vlinGit/Macropad/MacroPad/98db0589-fdbe-4938-8a90-1729ba8583cc.png

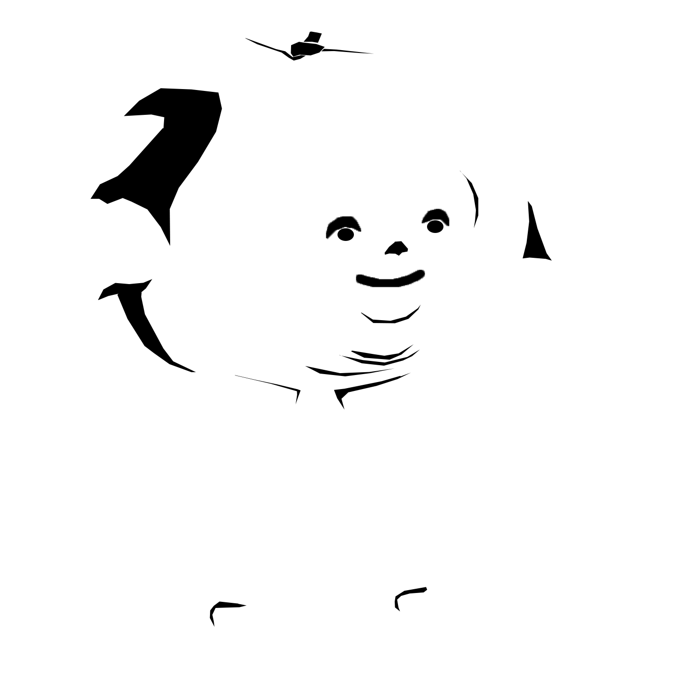
MacroPad/98db0589-fdbe-4938-8a90-1729ba8583cc.png
