vlinGit/Macropad/MacroPad/marbastlib-main/marbastlib-main/resources/repolist.png

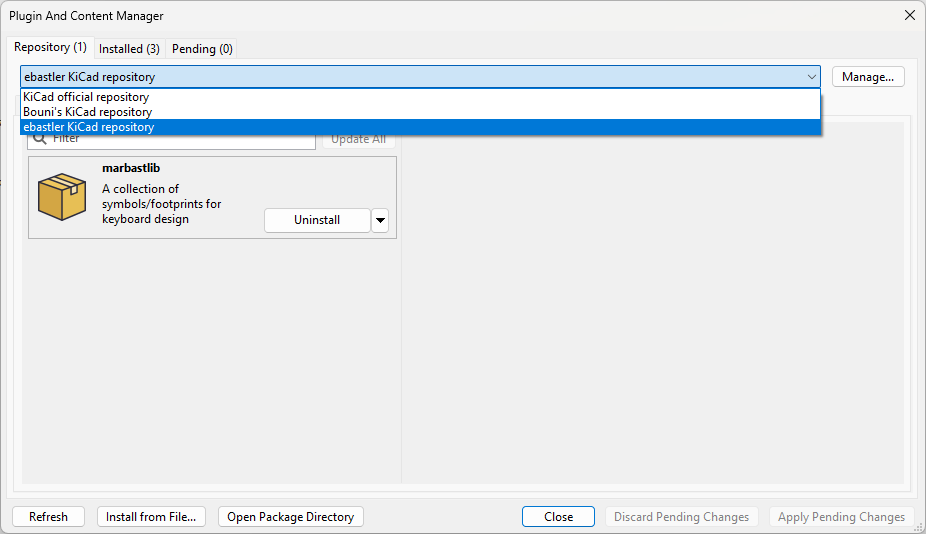
MacroPad/marbastlib-main/marbastlib-main/resources/repolist.png
