vlinGit/Macropad/MacroPad/simplePumpkin.png

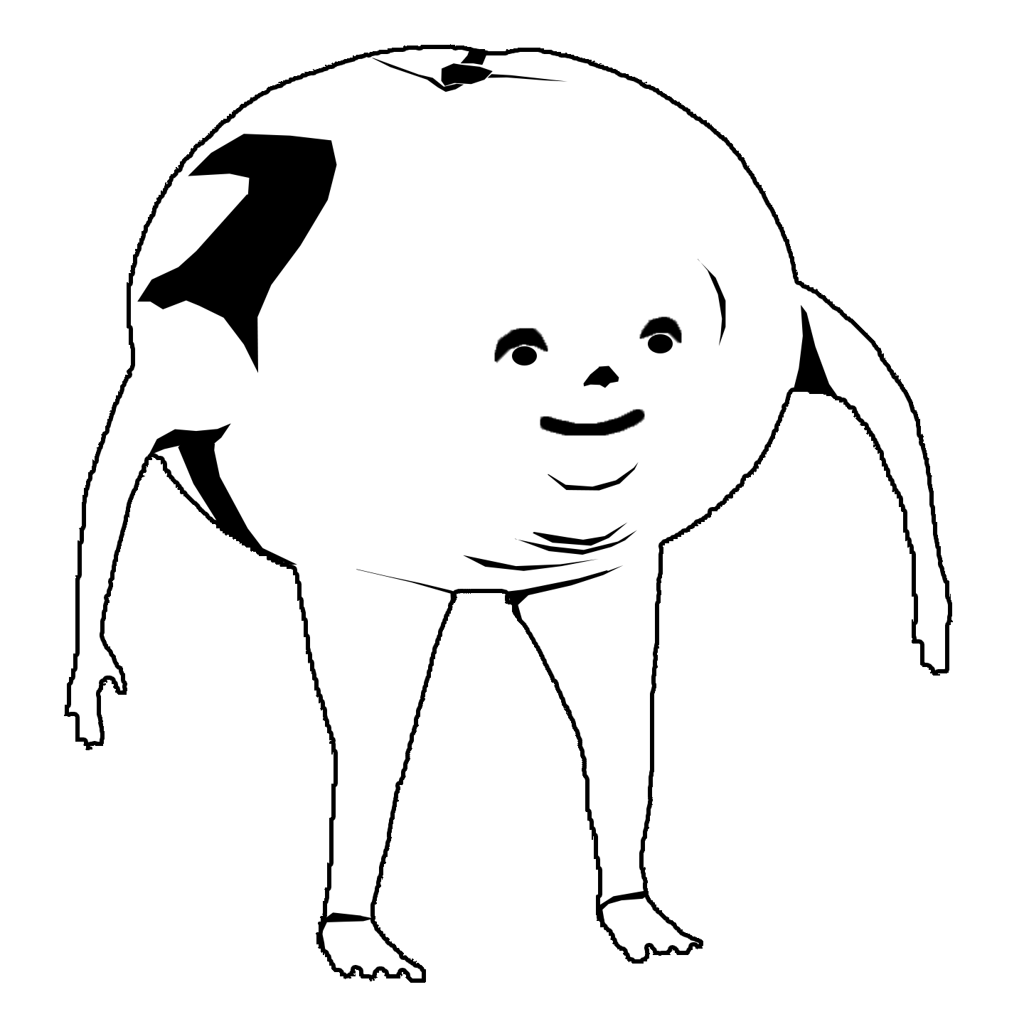
MacroPad/simplePumpkin.png
