vlinGit/Macropad/MacroPad/marbastlib-main/marbastlib-main/3dmodels/SW_SKHLLC.step

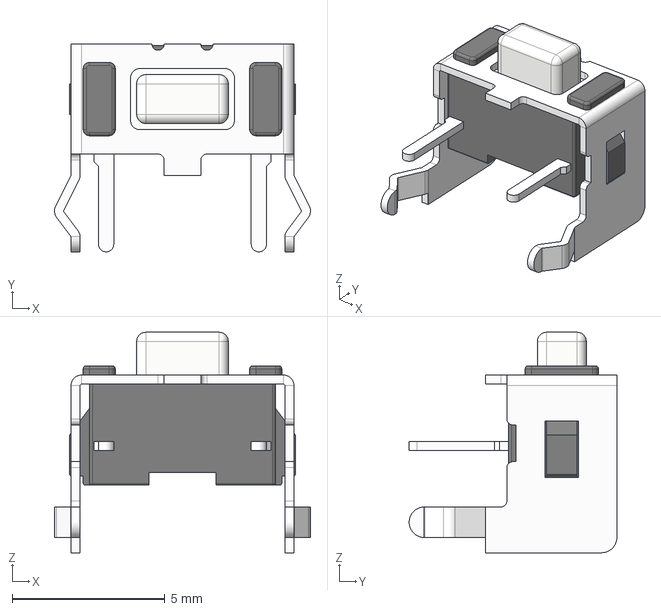
[picture p29: CAD file, 2024-05-07]
MacroPad/marbastlib-main/marbastlib-main/3dmodels/SW_SKHLLC.step
8.38 x 6.80 x 7.22 mm
