vlinGit/Macropad/MacroPad/marbastlib-main/marbastlib-main/3dmodels/SW_SSSS213100.step

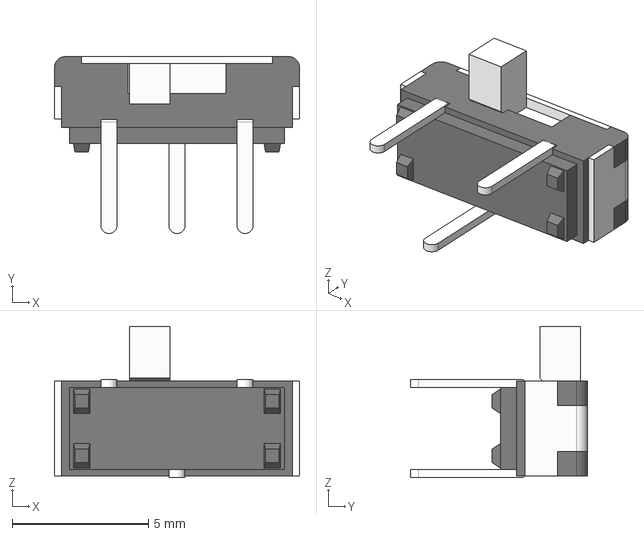
[picture p30: CAD file, 2024-05-07]
MacroPad/marbastlib-main/marbastlib-main/3dmodels/SW_SSSS213100.step
9.00 x 6.50 x 5.55 mm
