vlinGit/Macropad/MacroPad/marbastlib-main/marbastlib-main/3dmodels/PNT_psp1000.step

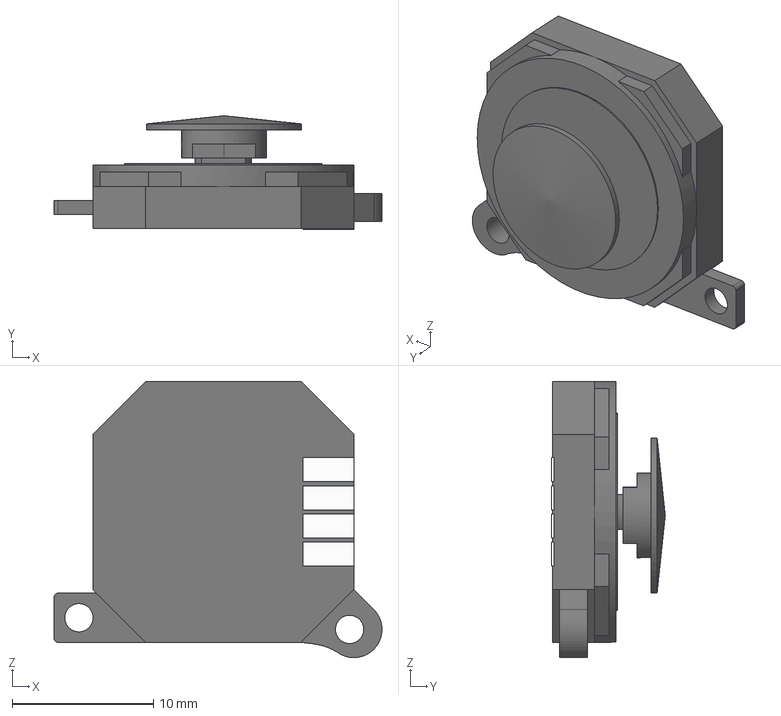
[picture p31: CAD file, 2024-05-07]
MacroPad/marbastlib-main/marbastlib-main/3dmodels/PNT_psp1000.step
23.2 x 8.05 x 19.6 mm
