vlinGit/Macropad/MacroPad/marbastlib-main/marbastlib-main/3dmodels/SW_MSK12C02.step

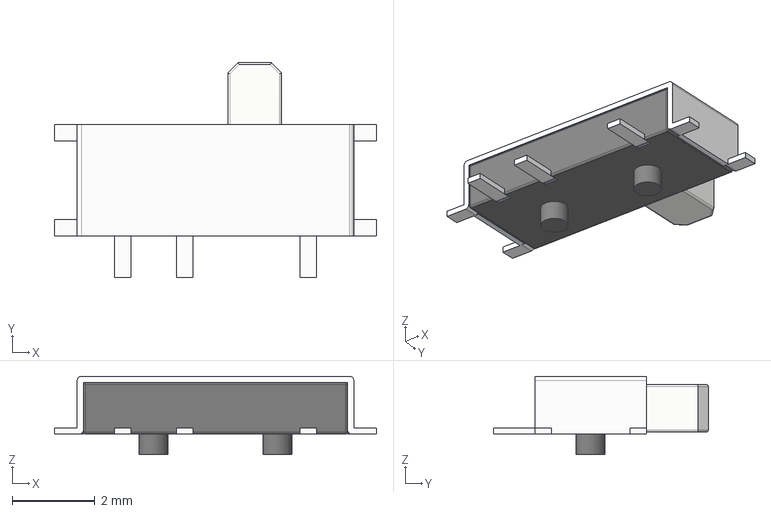
[picture p32: CAD file, 2024-05-07]
MacroPad/marbastlib-main/marbastlib-main/3dmodels/SW_MSK12C02.step
7.80 x 5.20 x 1.90 mm
