vlinGit/Macropad/MacroPad/marbastlib-main/marbastlib-main/3dmodels/ROT_EC11N.step

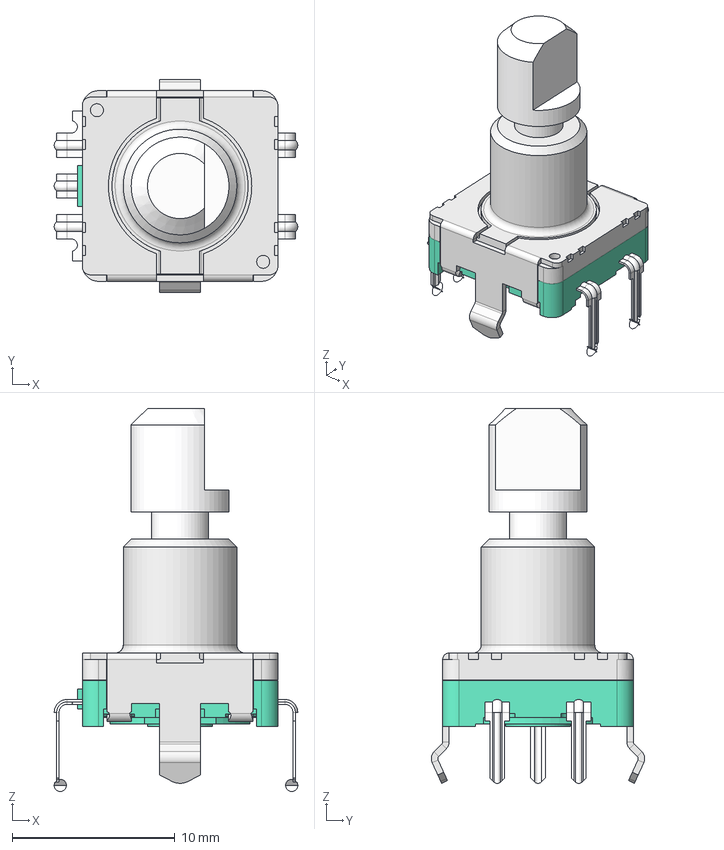
[picture p33: CAD file, 2024-05-07]
MacroPad/marbastlib-main/marbastlib-main/3dmodels/ROT_EC11N.step
14.9 x 13.1 x 23.5 mm
