vlinGit/Macropad/MacroPad/marbastlib-main/marbastlib-main/3dmodels/PNT_RKJXU1210006.step

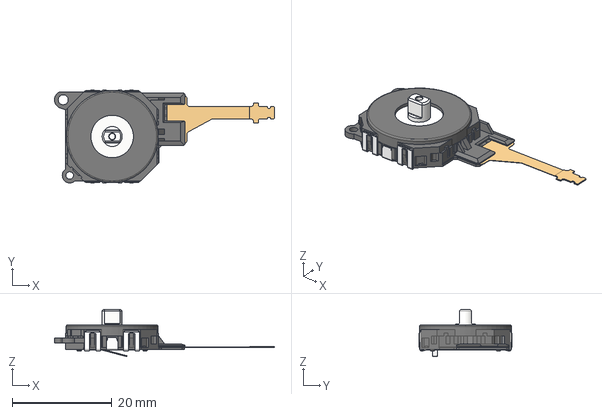
[picture p34: CAD file, 2024-05-07]
MacroPad/marbastlib-main/marbastlib-main/3dmodels/PNT_RKJXU1210006.step
44.0 x 18.6 x 9.50 mm
