vlinGit/Macropad/MacroPad/marbastlib-main/marbastlib-main/3dmodels/CON_BM02B-ACHSS.step

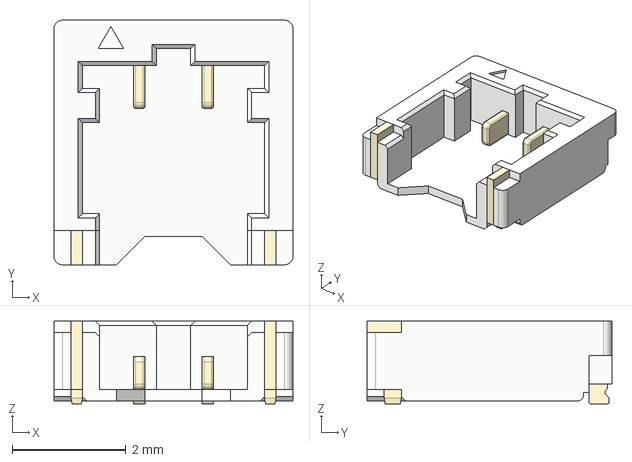
[picture p36: CAD file, 2024-05-07]
MacroPad/marbastlib-main/marbastlib-main/3dmodels/CON_BM02B-ACHSS.step
4.20 x 4.30 x 1.45 mm
