vlinGit/Macropad/MacroPad/marbastlib-main/marbastlib-main/3dmodels/Crystal_FA-128.step

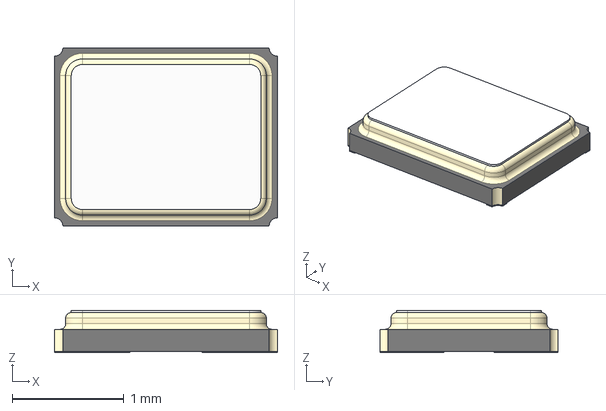
[picture p37: CAD file, 2024-05-07]
MacroPad/marbastlib-main/marbastlib-main/3dmodels/Crystal_FA-128.step
2.00 x 1.60 x 0.38 mm
