vlinGit/Macropad/MacroPad/marbastlib-main/marbastlib-main/3dmodels/CON_TYPE-C-31-M-14.step

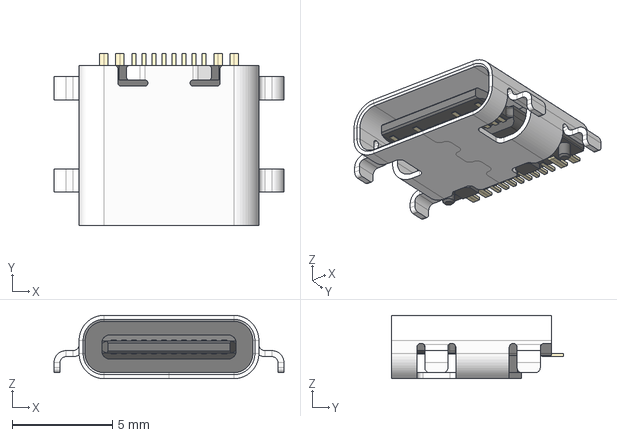
[picture p38: CAD file, 2024-05-07]
MacroPad/marbastlib-main/marbastlib-main/3dmodels/CON_TYPE-C-31-M-14.step
11.5 x 8.56 x 3.16 mm
Shroud
Plastic Body & Connector
