vlinGit/Macropad/MacroPad/marbastlib-main/marbastlib-main/3dmodels/LED_WS2812_2020.step

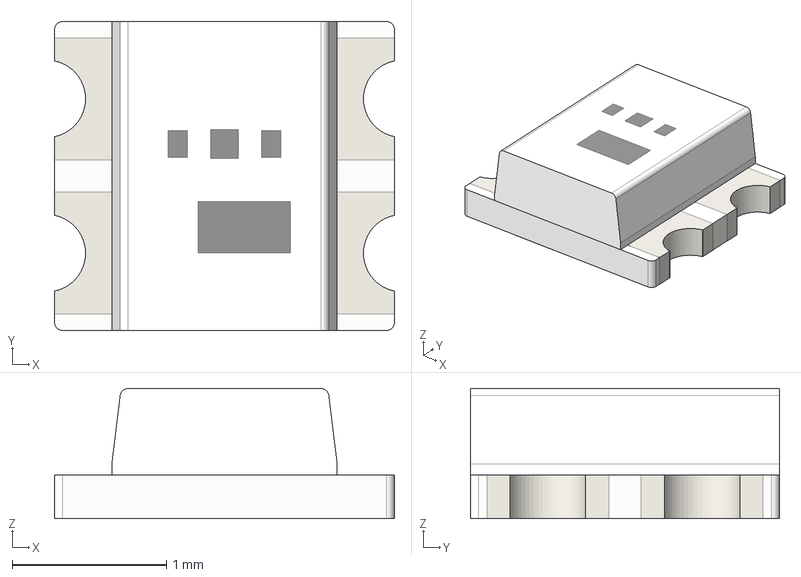
[picture p39: CAD file, 2024-05-07]
MacroPad/marbastlib-main/marbastlib-main/3dmodels/LED_WS2812_2020.step
2.20 x 2.00 x 0.842 mm
