vlinGit/Macropad/MacroPad/marbastlib-main/marbastlib-main/3dmodels/moko_mk08a_nRF52840.step

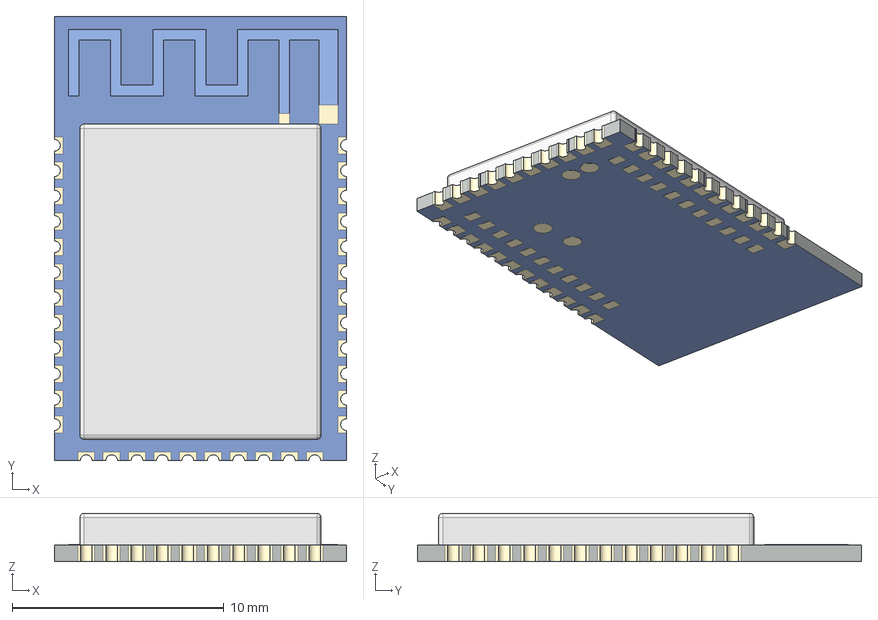
[picture p40: CAD file, 2024-05-07]
MacroPad/marbastlib-main/marbastlib-main/3dmodels/moko_mk08a_nRF52840.step
13.8 x 21.0 x 2.29 mm
