vlinGit/Macropad/MacroPad/marbastlib-main/marbastlib-main/3dmodels/HS_KS-2P02B01-01_MX.step

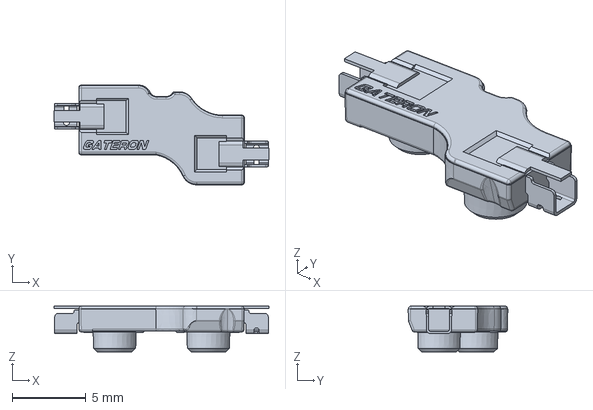
[picture p45: CAD file, 2024-05-07]
MacroPad/marbastlib-main/marbastlib-main/3dmodels/HS_KS-2P02B01-01_MX.step
14.6 x 6.74 x 3.10 mm
