vlinGit/Macropad/MacroPad/marbastlib-main/marbastlib-main/3dmodels/CON_SM13B-SRSS-TB.step

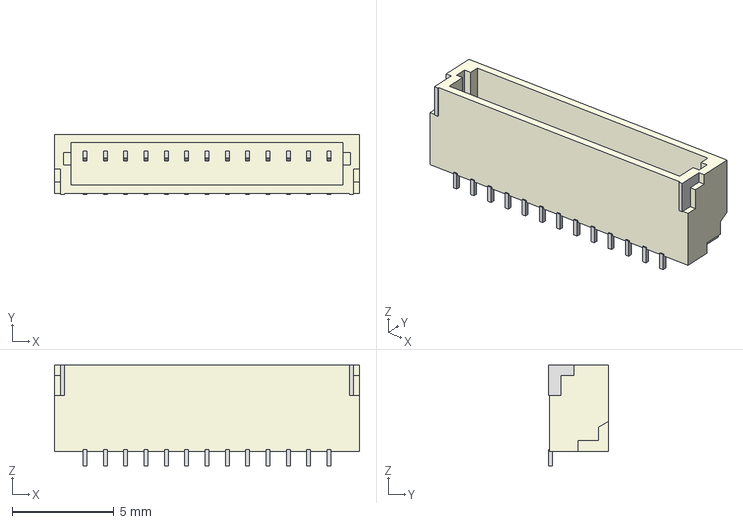
[picture p46: CAD file, 2024-05-07]
MacroPad/marbastlib-main/marbastlib-main/3dmodels/CON_SM13B-SRSS-TB.step
15.0 x 2.96 x 4.95 mm
