vlinGit/Macropad/MacroPad/marbastlib-main/marbastlib-main/3dmodels/Liatris.step

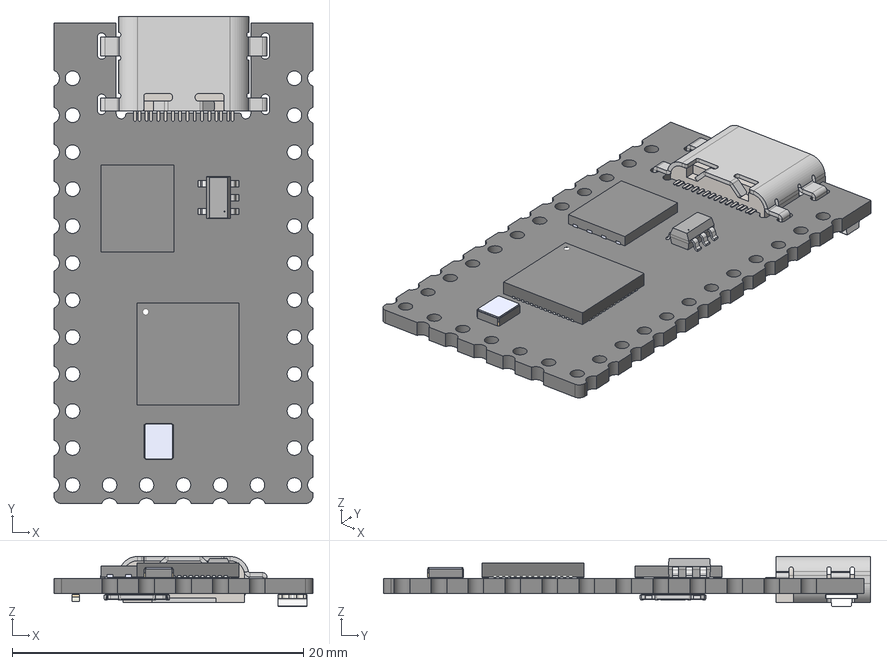
[picture p47: CAD file, 2024-05-07]
MacroPad/marbastlib-main/marbastlib-main/3dmodels/Liatris.step
17.8 x 33.5 x 3.44 mm
RP2040 PCB
