vlinGit/Macropad/MacroPad/marbastlib-main/marbastlib-main/3dmodels/SW_ESP3020.step

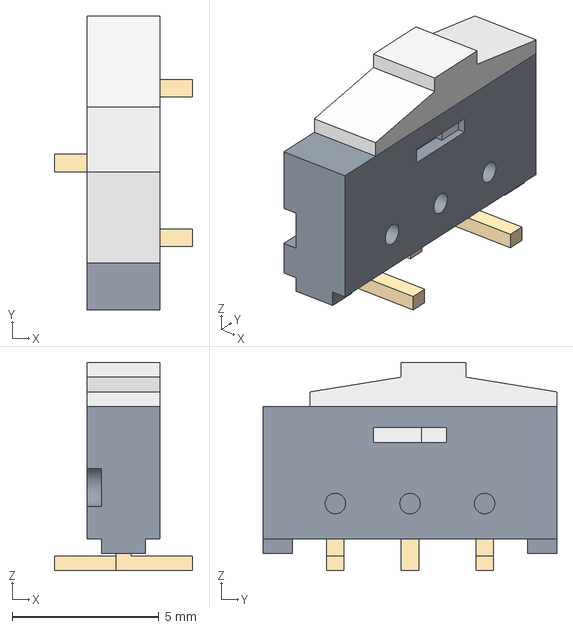
[picture p48: CAD file, 2024-05-07]
MacroPad/marbastlib-main/marbastlib-main/3dmodels/SW_ESP3020.step
4.70 x 10.0 x 7.08 mm
