vlinGit/Macropad/MacroPad/marbastlib-main/marbastlib-main/3dmodels/CON_SM02B-SRSS-TB.step

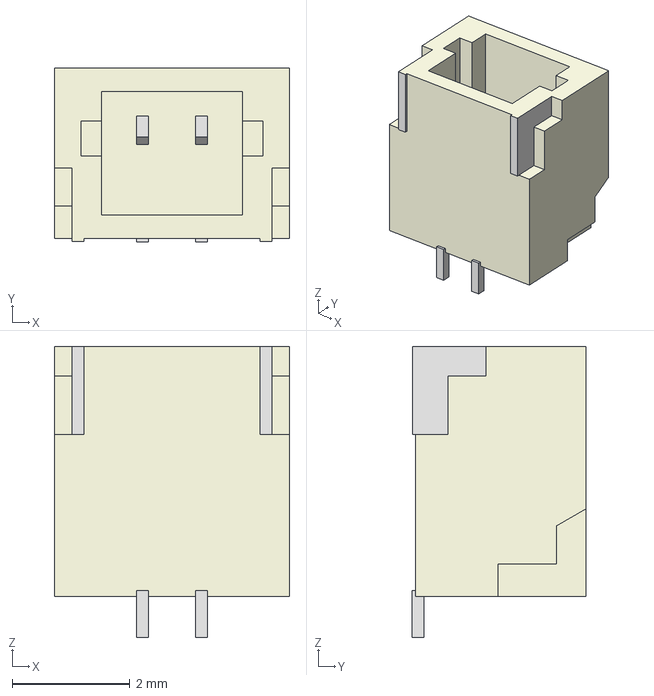
[picture p49: CAD file, 2024-05-07]
MacroPad/marbastlib-main/marbastlib-main/3dmodels/CON_SM02B-SRSS-TB.step
4.00 x 2.96 x 4.95 mm
