vlinGit/Macropad/MacroPad/marbastlib-main/marbastlib-main/3dmodels/LED_SK6812MINI-E.step

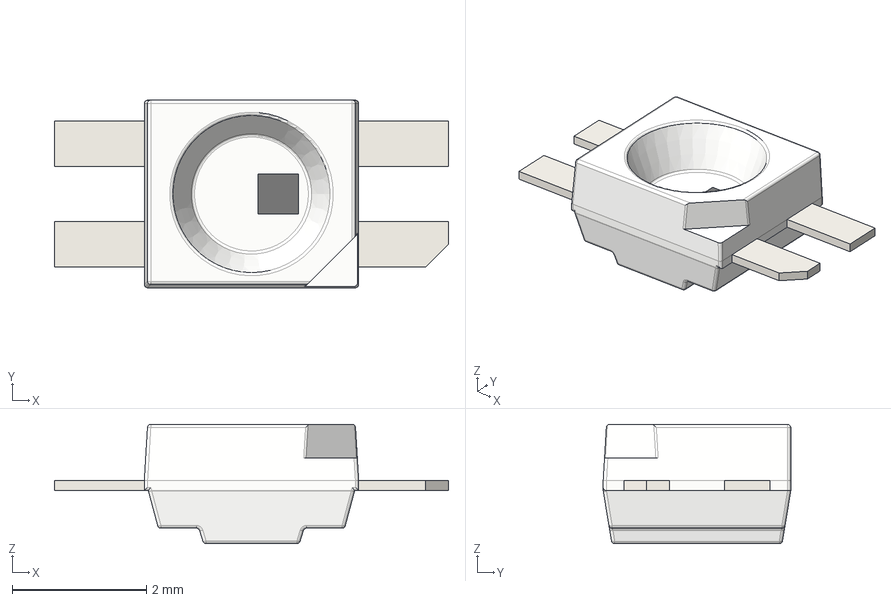
[picture p50: CAD file, 2024-05-07]
MacroPad/marbastlib-main/marbastlib-main/3dmodels/LED_SK6812MINI-E.step
5.88 x 2.80 x 1.78 mm
