vlinGit/Macropad/MacroPad/marbastlib-main/marbastlib-main/3dmodels/CON_781710002.step

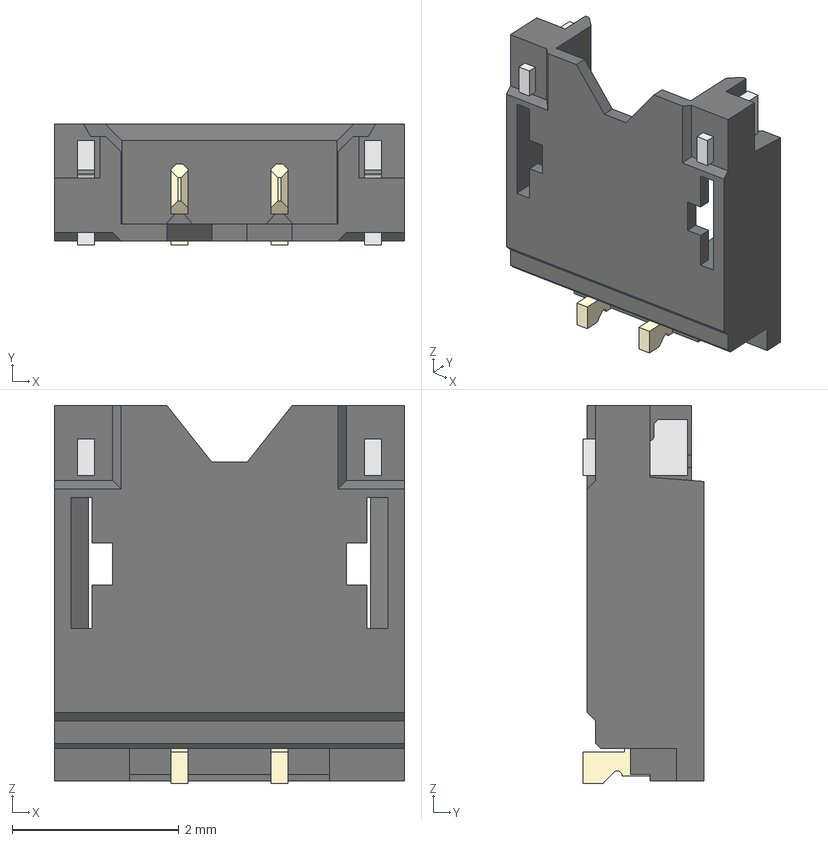
[picture p51: CAD file, 2024-05-07]
MacroPad/marbastlib-main/marbastlib-main/3dmodels/CON_781710002.step
4.20 x 1.45 x 4.53 mm
