vlinGit/Macropad/MacroPad/marbastlib-main/marbastlib-main/3dmodels/CON_2121340006.step

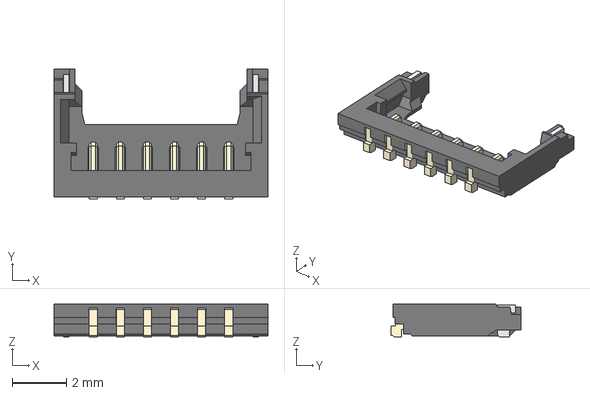
[picture p54: CAD file, 2024-05-07]
MacroPad/marbastlib-main/marbastlib-main/3dmodels/CON_2121340006.step
7.90 x 4.79 x 1.20 mm
