vlinGit/Macropad/MacroPad/marbastlib-main/marbastlib-main/3dmodels/CON_781710005.step

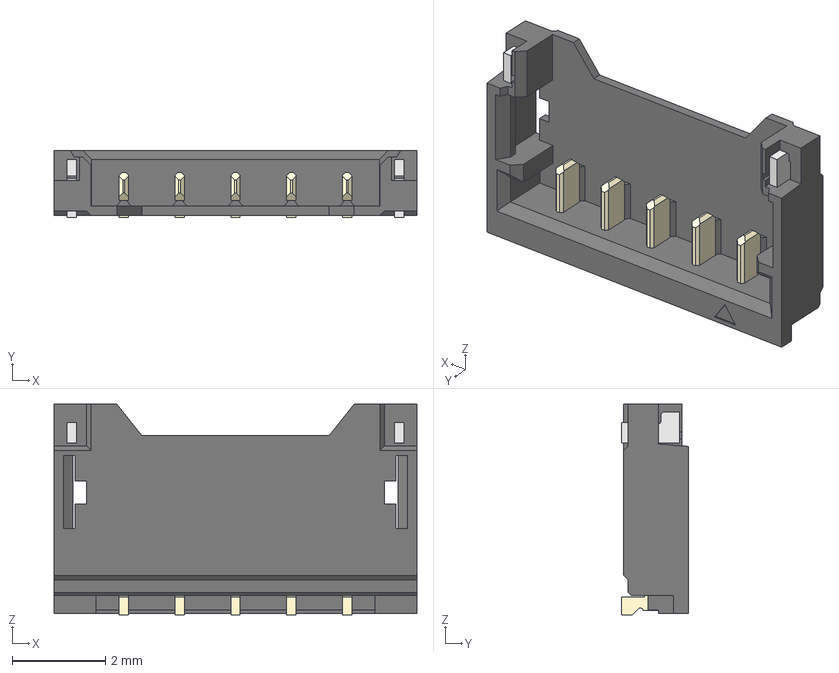
[picture p55: CAD file, 2024-05-07]
MacroPad/marbastlib-main/marbastlib-main/3dmodels/CON_781710005.step
7.80 x 1.45 x 4.53 mm
