vlinGit/Macropad/MacroPad/marbastlib-main/marbastlib-main/3dmodels/CON_2121340004.step

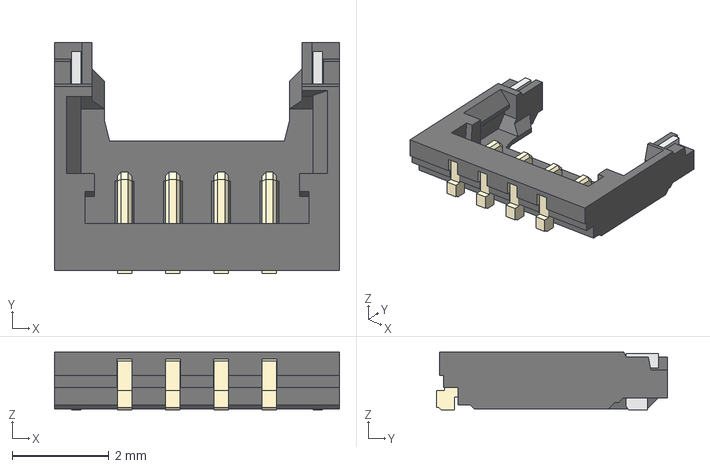
[picture p56: CAD file, 2024-05-07]
MacroPad/marbastlib-main/marbastlib-main/3dmodels/CON_2121340004.step
5.90 x 4.79 x 1.20 mm
