vlinGit/Macropad/MacroPad/marbastlib-main/marbastlib-main/3dmodels/CON_2082940050.step

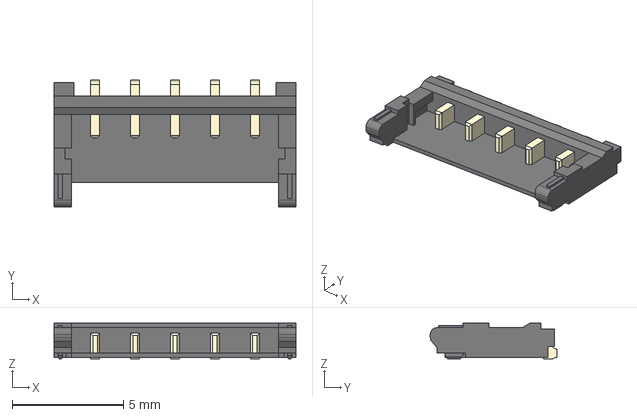
[picture p57: CAD file, 2024-05-07]
MacroPad/marbastlib-main/marbastlib-main/3dmodels/CON_2082940050.step
10.9 x 5.70 x 1.60 mm
