vlinGit/Macropad/MacroPad/marbastlib-main/marbastlib-main/3dmodels/CON_SM07B-SRSS-TB.step

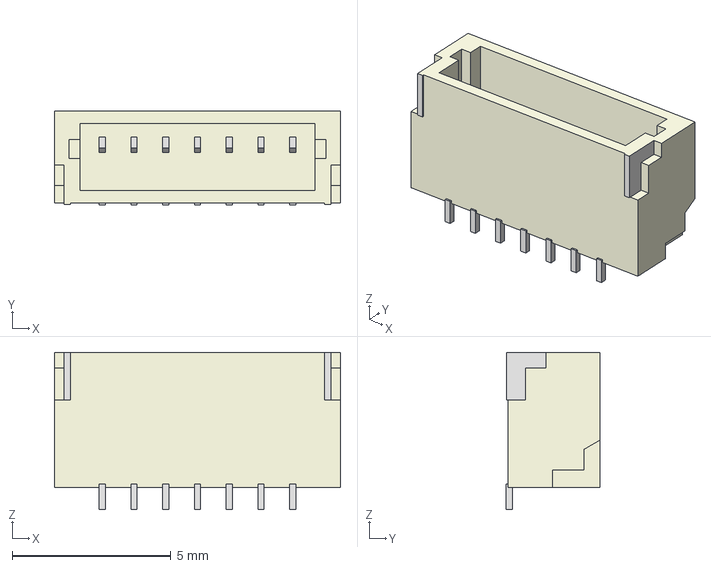
[picture p58: CAD file, 2024-05-07]
MacroPad/marbastlib-main/marbastlib-main/3dmodels/CON_SM07B-SRSS-TB.step
9.00 x 2.96 x 4.95 mm
