vlinGit/Macropad/MacroPad/marbastlib-main/marbastlib-main/3dmodels/LED_WS2812B-MINI.step

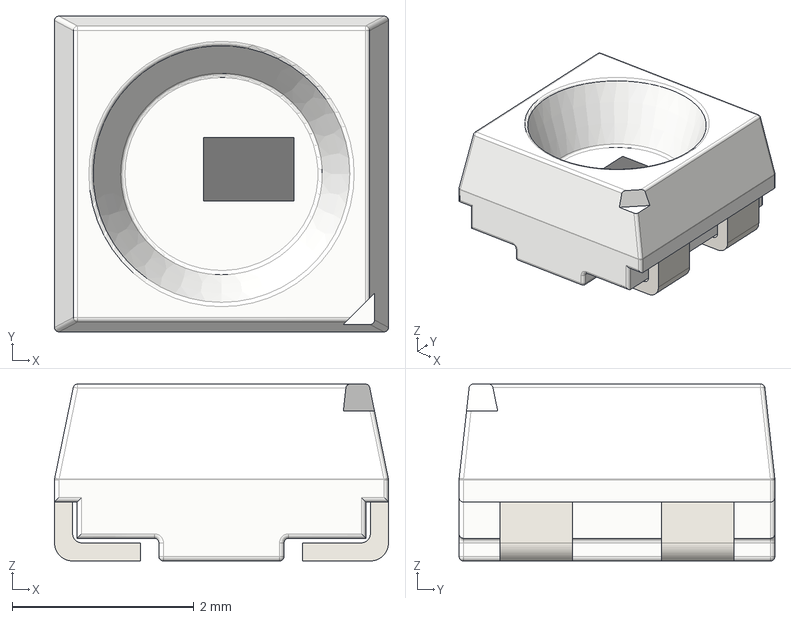
[picture p59: CAD file, 2024-05-07]
MacroPad/marbastlib-main/marbastlib-main/3dmodels/LED_WS2812B-MINI.step
3.68 x 3.48 x 1.95 mm
