vlinGit/Macropad/MacroPad/marbastlib-main/marbastlib-main/3dmodels/CON_781710003.step

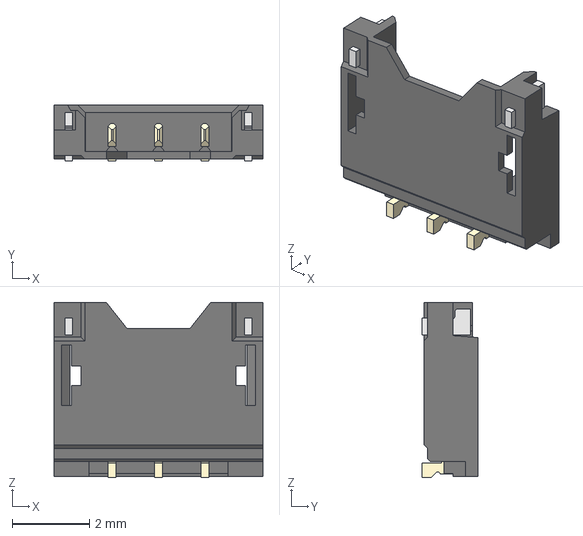
[picture p60: CAD file, 2024-05-07]
MacroPad/marbastlib-main/marbastlib-main/3dmodels/CON_781710003.step
5.40 x 1.45 x 4.53 mm
