vlinGit/Macropad/MacroPad/marbastlib-main/marbastlib-main/3dmodels/CON_SM06B-SRSS-TB.step

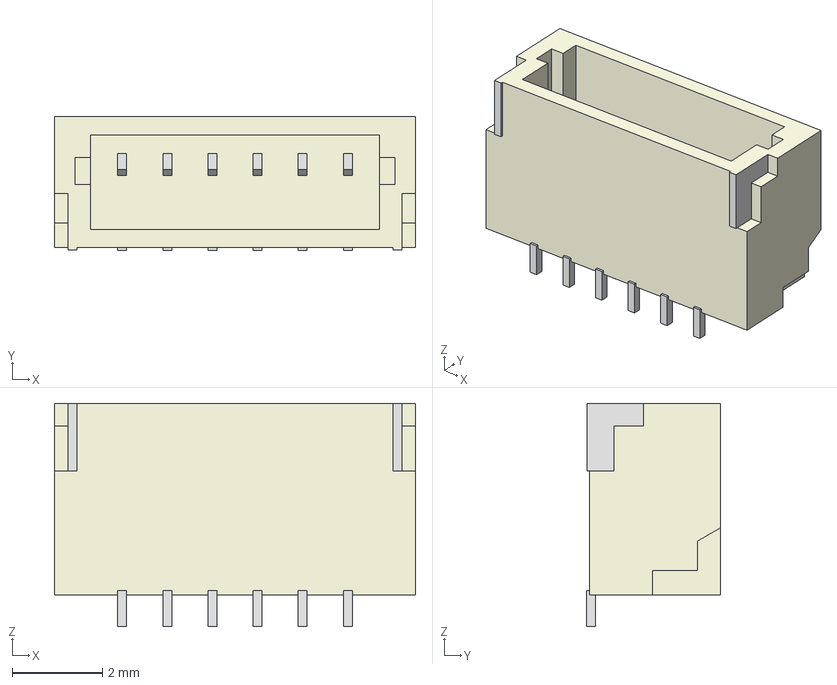
[picture p61: CAD file, 2024-05-07]
MacroPad/marbastlib-main/marbastlib-main/3dmodels/CON_SM06B-SRSS-TB.step
8.00 x 2.96 x 4.95 mm
