vlinGit/Macropad/MacroPad/marbastlib-main/marbastlib-main/3dmodels/ROT_SKYLOONG_HS.step

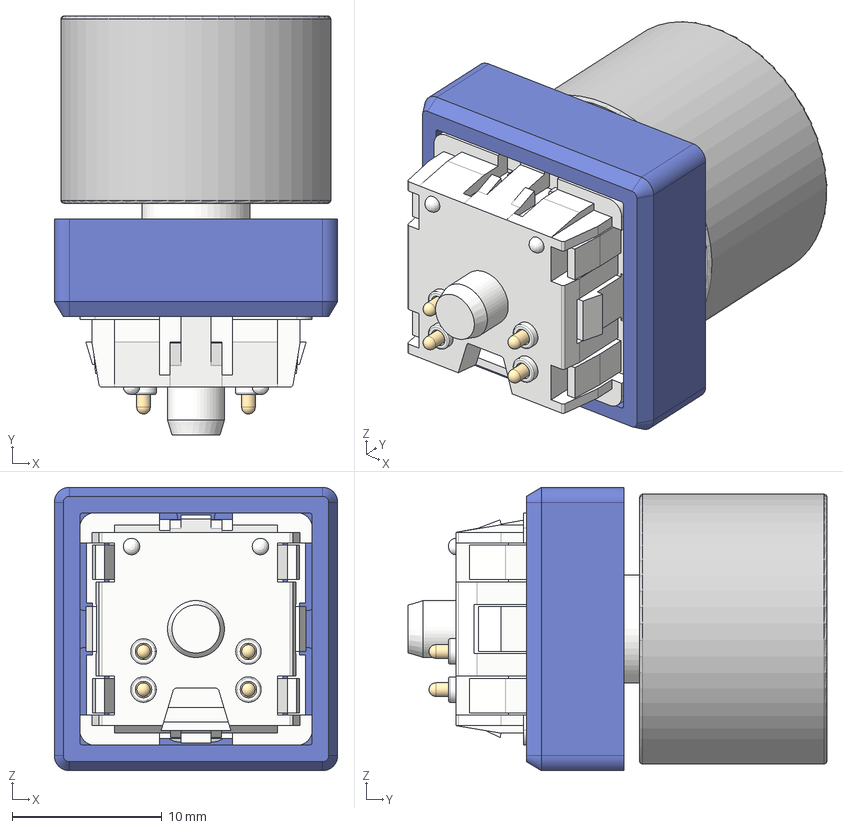
[picture p62: CAD file, 2024-05-07]
MacroPad/marbastlib-main/marbastlib-main/3dmodels/ROT_SKYLOONG_HS.step
18.9 x 27.9 x 18.9 mm
Top
Shaft
Pogo Pin x 4
Bottom
Top_1
Cover
Knob
