vlinGit/Macropad/MacroPad/marbastlib-main/marbastlib-main/3dmodels/CON_XUNPU_FPC-05F-16PH20.step

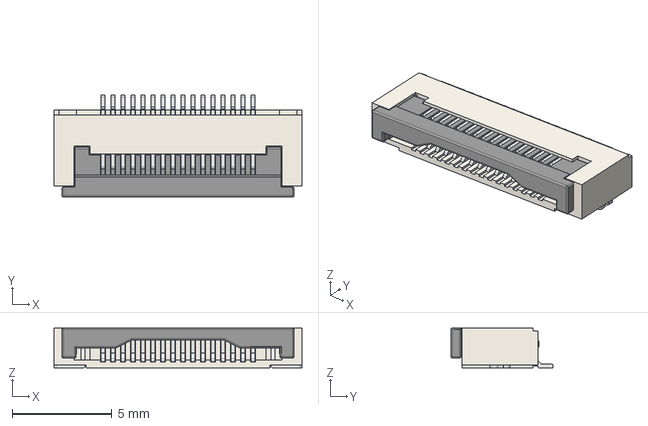
[picture p63: CAD file, 2024-05-07]
MacroPad/marbastlib-main/marbastlib-main/3dmodels/CON_XUNPU_FPC-05F-16PH20.step
12.4 x 5.12 x 2.00 mm
