vlinGit/Macropad/MacroPad/marbastlib-main/marbastlib-main/3dmodels/ROT_EC11E.step

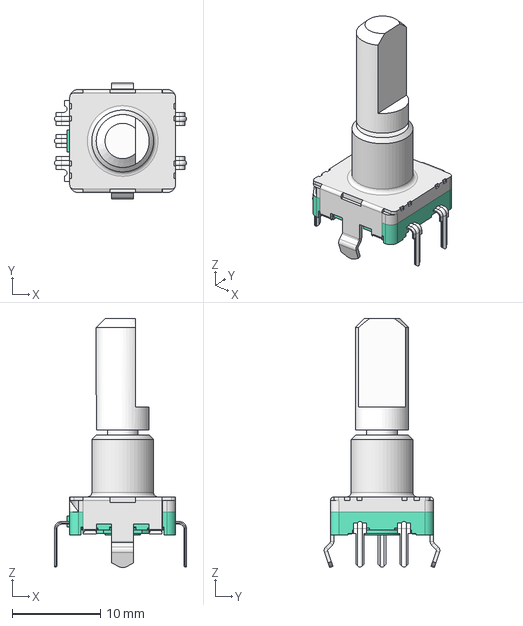
[picture p64: CAD file, 2024-05-07]
MacroPad/marbastlib-main/marbastlib-main/3dmodels/ROT_EC11E.step
14.9 x 13.1 x 28.2 mm
