vlinGit/Macropad/MacroPad/marbastlib-main/marbastlib-main/3dmodels/CON_2082940040.step

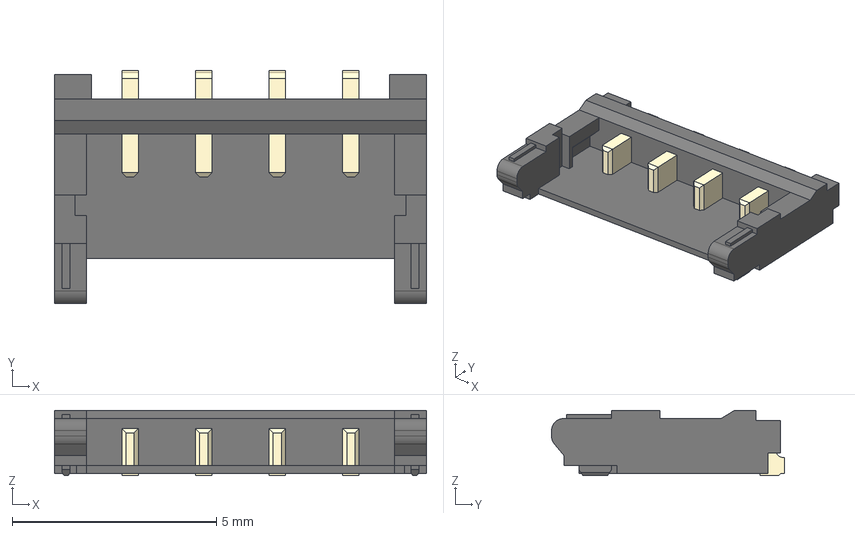
[picture p66: CAD file, 2024-05-07]
MacroPad/marbastlib-main/marbastlib-main/3dmodels/CON_2082940040.step
9.10 x 5.70 x 1.60 mm
