vlinGit/Macropad/MacroPad/marbastlib-main/marbastlib-main/3dmodels/holyiot_18010_nRF52840.step

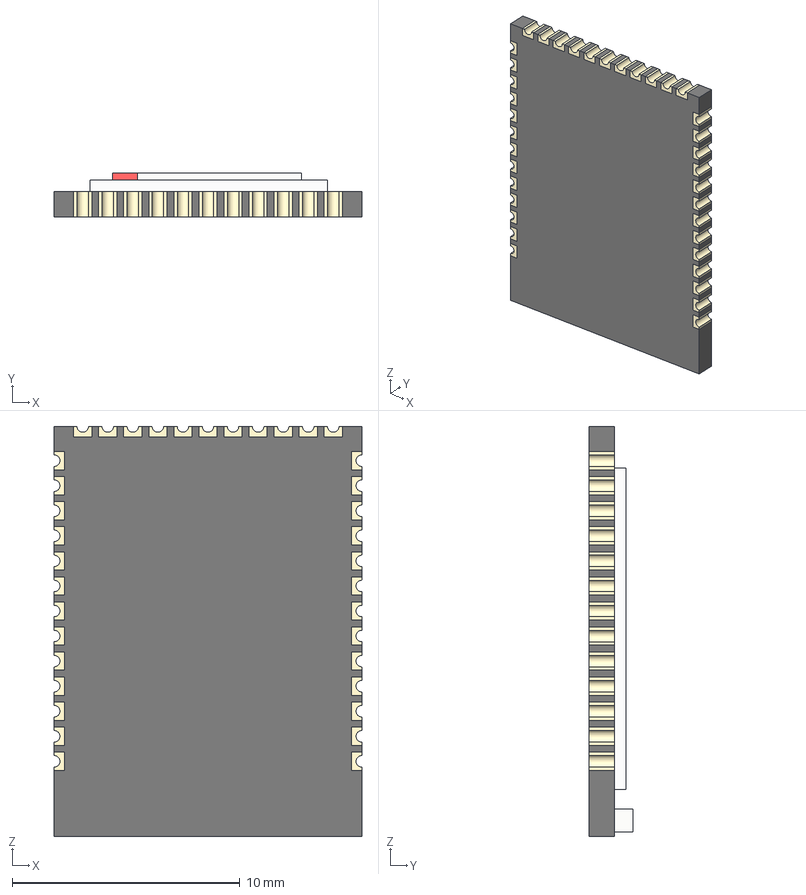
[picture p67: CAD file, 2024-05-07]
MacroPad/marbastlib-main/marbastlib-main/3dmodels/holyiot_18010_nRF52840.step
13.5 x 1.92 x 18.0 mm
