vlinGit/Macropad/MacroPad/marbastlib-main/marbastlib-main/3dmodels/CON_2082940030.step

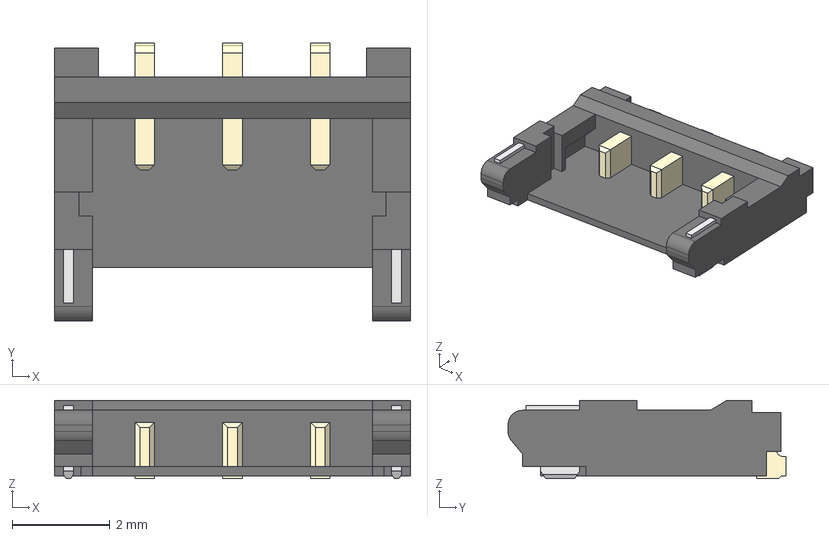
[picture p68: CAD file, 2024-05-07]
MacroPad/marbastlib-main/marbastlib-main/3dmodels/CON_2082940030.step
7.30 x 5.70 x 1.60 mm
