vlinGit/Macropad/MacroPad/marbastlib-main/marbastlib-main/3dmodels/CON_781710004.step

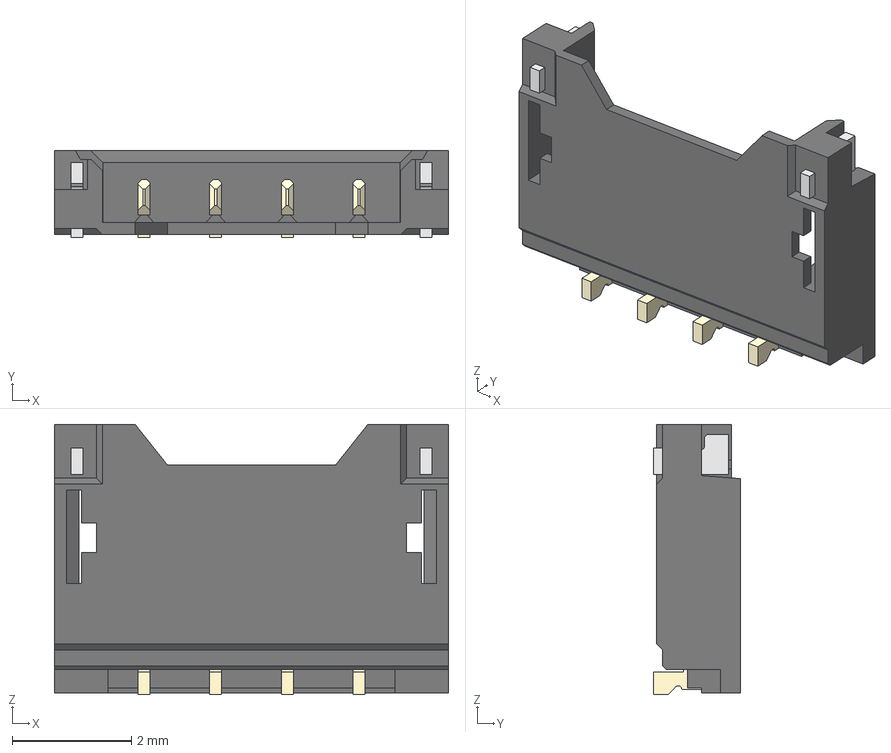
[picture p69: CAD file, 2024-05-07]
MacroPad/marbastlib-main/marbastlib-main/3dmodels/CON_781710004.step
6.60 x 1.45 x 4.53 mm
