vlinGit/Macropad/MacroPad/marbastlib-main/marbastlib-main/3dmodels/HS_KS-2P02B01-02_KS33.step

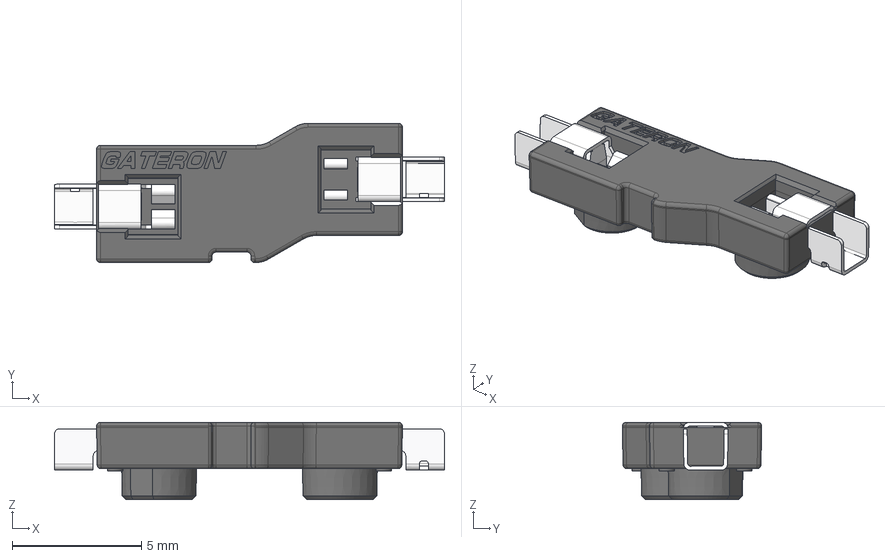
[picture p70: CAD file, 2024-05-07]
MacroPad/marbastlib-main/marbastlib-main/3dmodels/HS_KS-2P02B01-02_KS33.step
15.1 x 5.39 x 3.00 mm
